CoretechR/ESP32-Handheld/Memo/bmp.h

// 'Bluetooth_bmp', 6x12px
const unsigned char bluetooth_bmp [] PROGMEM = {
  0x20, 0x30, 0x28, 0xa4, 0x68, 0x30, 0x30, 0x68, 0xa4, 0x28, 0x30, 0x20
};
// 'calc_bmp', 48x48px
const unsigned char calc_bmp [] PROGMEM = {
  0x03, 0xff, 0xff, 0xff, 0xff, 0xc0, 0x0f, 0xff, 0xff, 0xff, 0xff, 0xf0, 0x1f, 0xff, 0xff, 0xff, 
  0xff, 0xf8, 0x3f, 0xff, 0xff, 0xff, 0xff, 0xfc, 0x7f, 0xff, 0xff, 0xff, 0xff, 0xfe, 0x7f, 0xff, 
  0xff, 0xff, 0xff, 0xfe, 0xff, 0xff, 0xff, 0xff, 0xff, 0xff, 0xff, 0xff, 0xff, 0xff, 0xff, 0xff, 
  0xff, 0xe3, 0xff, 0xff, 0xff, 0xff, 0xff, 0xe3, 0xff, 0xff, 0xff, 0xff, 0xff, 0xe3, 0xff, 0xff, 
  0xff, 0xff, 0xff, 0xe3, 0xff, 0xff, 0xff, 0xff, 0xfe, 0x00, 0x3f, 0xf0, 0x01, 0xff, 0xfe, 0x00, 
  0x3f, 0xf0, 0x01, 0xff, 0xfe, 0x00, 0x3f, 0xf0, 0x01, 0xff, 0xff, 0xe3, 0xff, 0xff, 0xff, 0xff, 
  0xff, 0xe3, 0xff, 0xff, 0xff, 0xff, 0xff, 0xe3, 0xff, 0xff, 0xff, 0xff, 0xff, 0xe3, 0xff, 0xff, 
  0xff, 0xff, 0xff, 0xff, 0xff, 0xff, 0xff, 0xff, 0xff, 0xff, 0xff, 0xff, 0xff, 0xff, 0xff, 0xff, 
  0xff, 0xff, 0xff, 0xff, 0xff, 0xff, 0xff, 0xff, 0xff, 0xff, 0xff, 0xff, 0xff, 0xff, 0xff, 0xff, 
  0xff, 0xff, 0xff, 0xff, 0xff, 0xff, 0xff, 0xff, 0xff, 0xff, 0xff, 0xff, 0xff, 0xff, 0xff, 0xff, 
  0xff, 0xff, 0xff, 0xff, 0xff, 0xff, 0xff, 0xff, 0xff, 0xff, 0xff, 0xff, 0xff, 0xff, 0xff, 0xbe, 
  0xff, 0xff, 0xbf, 0xff, 0xff, 0x1c, 0x7f, 0xff, 0x1f, 0xff, 0xff, 0x08, 0x7f, 0xff, 0xbf, 0xff, 
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
  0x1f, 0x00, 0x00, 0x00, 0x00, 0x00, 0x3e, 0x00, 0x0f, 0xe0, 0x00, 0x00, 0x00, 0x01, 0xfc, 0x00, 
  0x07, 0xe0, 0x00, 0x00, 0x00, 0x01, 0xf8, 0x00, 0x01, 0xe0, 0x00, 0x00, 0x00, 0x01, 0xe0, 0x00
};
// 'pointer', 17x25px
const unsigned char pointer [] PROGMEM = {
  0x80, 0x00, 0x00, 0xc0, 0x00, 0x00, 0xe0, 0x00, 0x00, 0xf0, 0x00, 0x00, 0xf8, 0x00, 0x00, 0xfc, 
  0x00, 0x00, 0xfe, 0x00, 0x00, 0xff, 0x00, 0x00, 0xff, 0x80, 0x00, 0xff, 0xc0, 0x00, 0xff, 0xe0, 
  0x00, 0xff, 0xf0, 0x00, 0xff, 0xf8, 0x00, 0xff, 0xfc, 0x00, 0xff, 0xfe, 0x00, 0xff, 0xff, 0x00, 
  0xff, 0xff, 0x80, 0xff, 0xff, 0x80, 0xfc, 0x00, 0x00, 0xf8, 0x00, 0x00, 0xf8, 0x00, 0x00, 0xf0, 
  0x00, 0x00, 0xe0, 0x00, 0x00, 0xc0, 0x00, 0x00, 0x80, 0x00, 0x00
};
